mcheah/Rostock_Mini_Pro_2/sources_step/plate_spacer.step

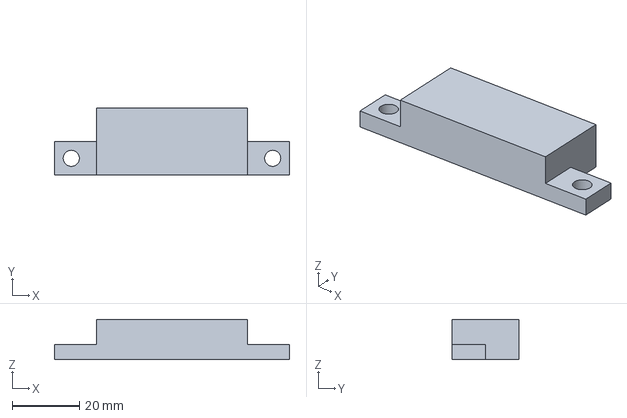
[picture p15: CAD file, 2026-03-06]
sources_step/plate_spacer.step
70.0 x 20.0 x 12.0 mm
