mcheah/Rostock_Mini_Pro_2/sources_step/filament_holder_topmount.step

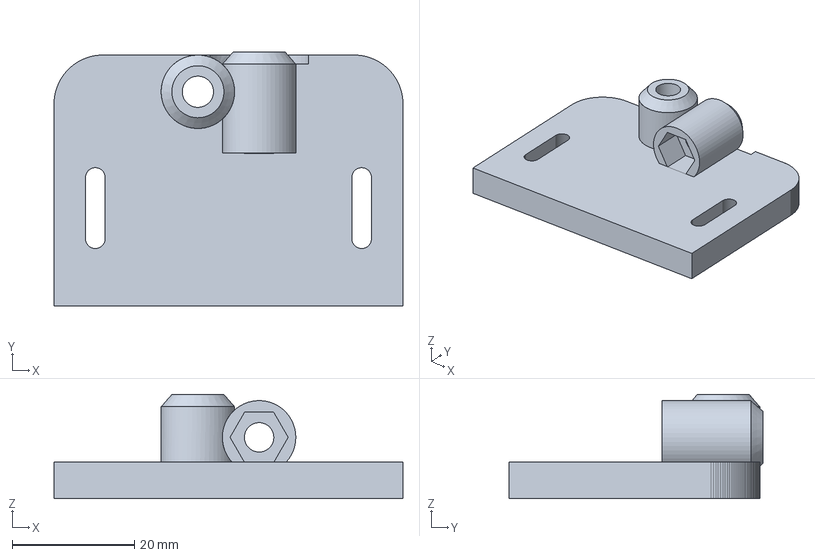
[picture p16: CAD file, 2026-03-06]
sources_step/filament_holder_topmount.step
57.0 x 41.5 x 17.0 mm
