mcheah/Rostock_Mini_Pro_2/sources_step/frame.step

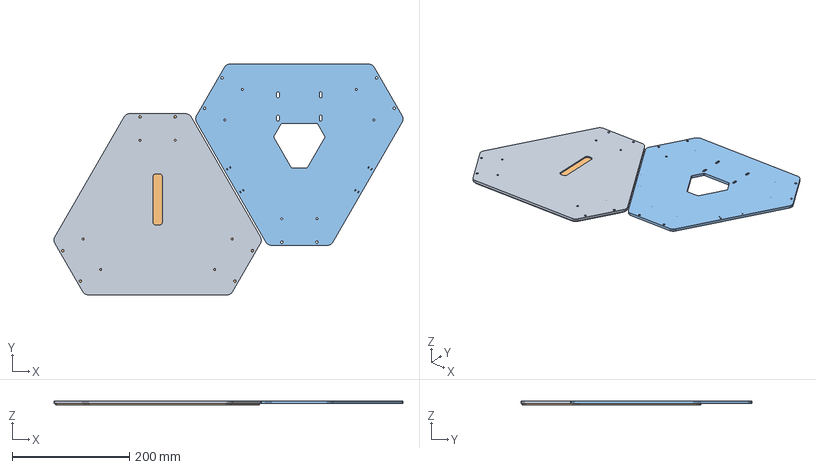
[picture p17: CAD file, 2026-03-06]
sources_step/frame.step
596.4 x 394.8 x 7.50 mm
minkowski003
