mcheah/Rostock_Mini_Pro_2/sources_step/endstop_template.step

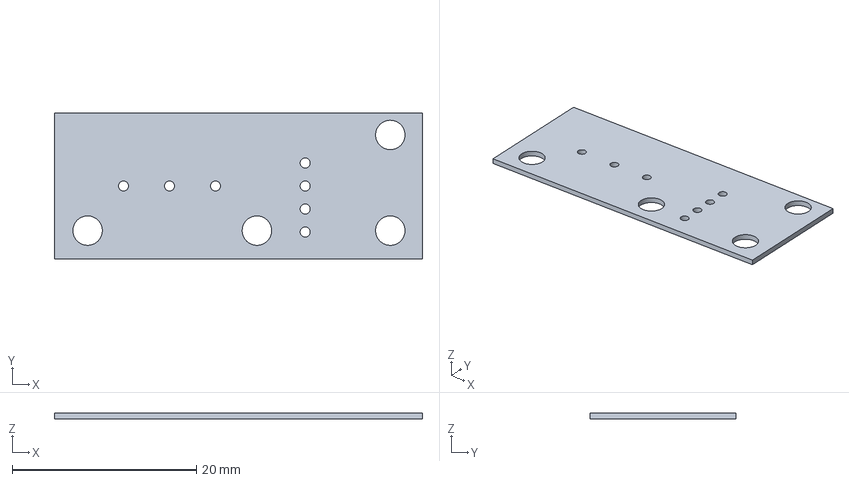
[picture p18: CAD file, 2026-03-06]
sources_step/endstop_template.step
40.0 x 15.9 x 0.65 mm
