mcheah/Rostock_Mini_Pro_2/sources_step/fan_mount.step

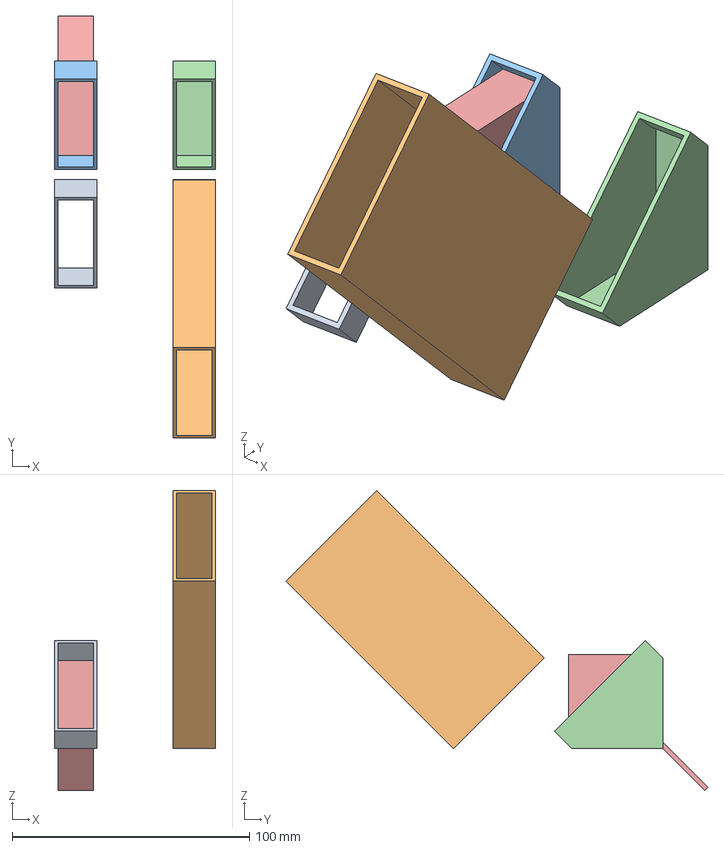
[picture p19: CAD file, 2026-03-06]
sources_step/fan_mount.step
68.0 x 178.1 x 126.6 mm
