mcheah/Rostock_Mini_Pro_2/sources_step/hotend_mount.step

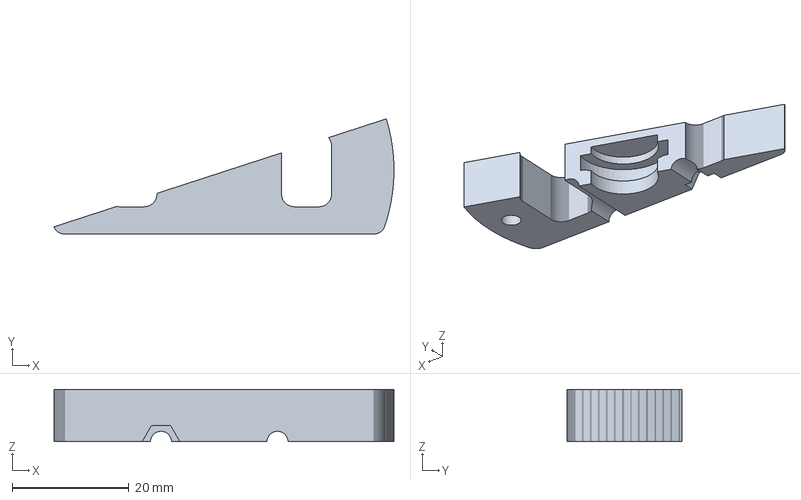
[picture p20: CAD file, 2026-02-26]
sources_step/hotend_mount.step
58.4 x 19.8 x 9.00 mm
