mcheah/Rostock_Mini_Pro_2/sources_step/hotend_mount_spacer.step

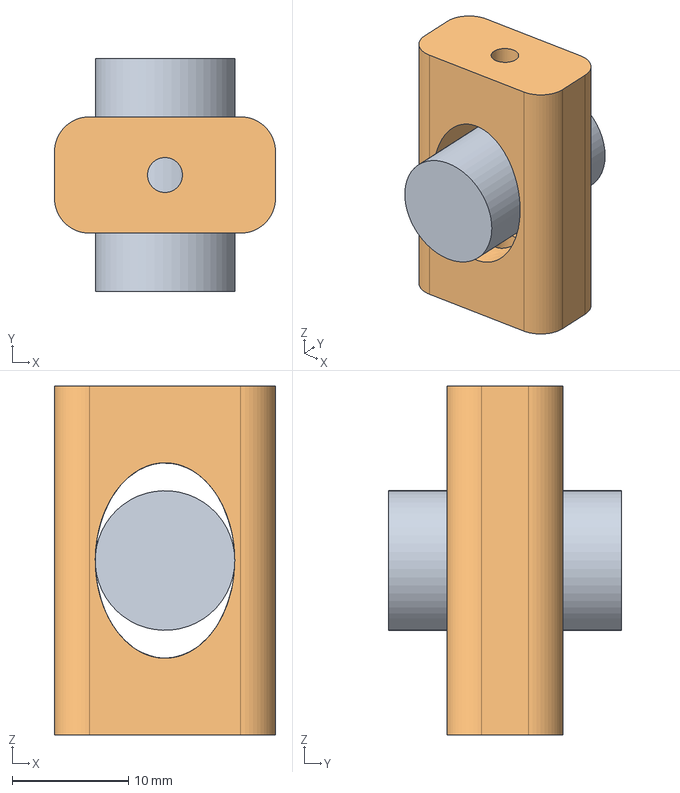
[picture p21: CAD file, 2026-02-26]
sources_step/hotend_mount_spacer.step
19.0 x 20.0 x 30.0 mm
