mcheah/Rostock_Mini_Pro_2/sources_step/plate_top.step

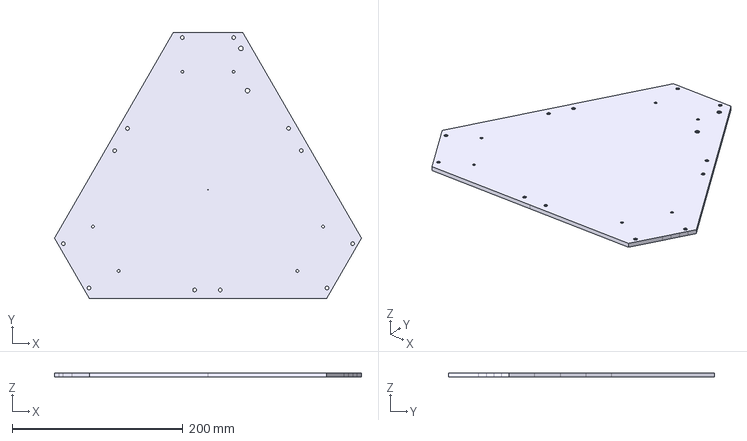
[picture p22: CAD file, 2026-02-26]
sources_step/plate_top.step
359.3 x 311.2 x 5.00 mm
