mcheah/Rostock_Mini_Pro_2/sources_step/motor_end_standoff.step

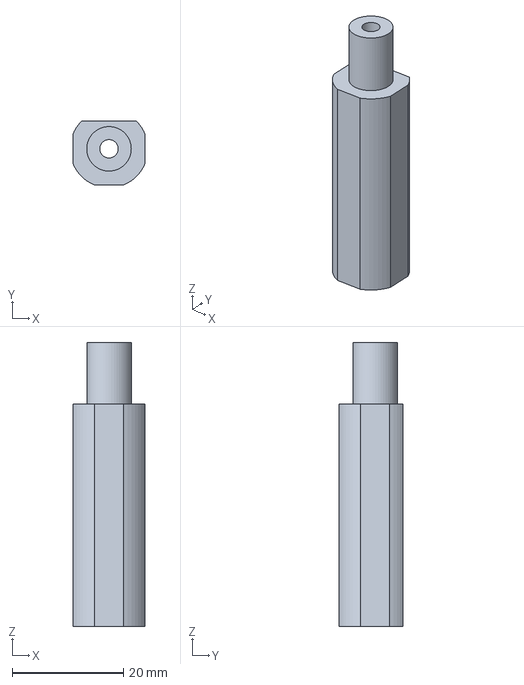
[picture p23: CAD file, 2026-02-26]
sources_step/motor_end_standoff.step
13.0 x 11.5 x 51.0 mm
