mcheah/Rostock_Mini_Pro_2/sources_step/filament_holder.step

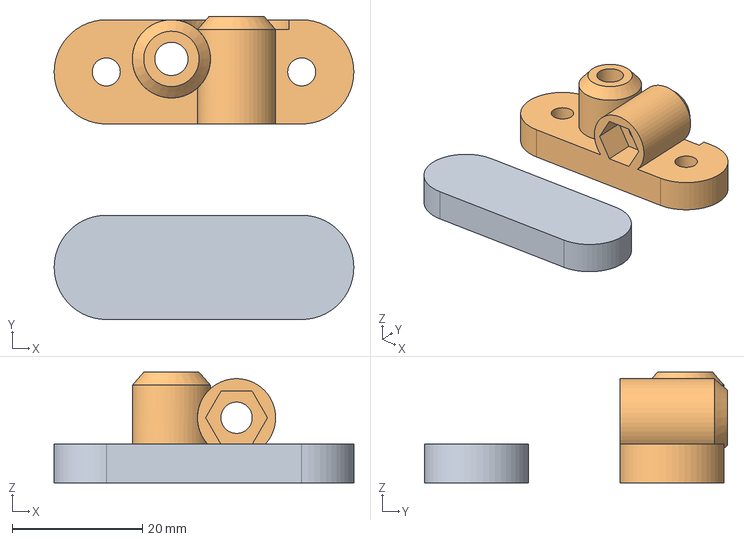
[picture p24: CAD file, 2026-02-26]
sources_step/filament_holder.step
46.0 x 46.5 x 17.0 mm
