mcheah/Rostock_Mini_Pro_2/sources_step/debug_drive_with_carriage.step

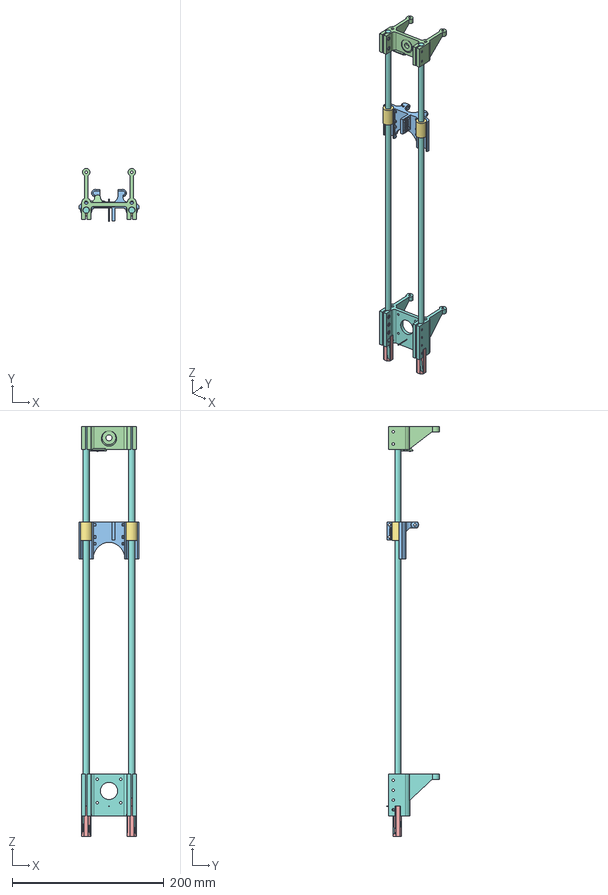
[picture p25: CAD file, 2026-02-26]
sources_step/debug_drive_with_carriage.step
79.0 x 70.0 x 540.0 mm
