mcheah/Rostock_Mini_Pro_2/sources_step/motor_end.step

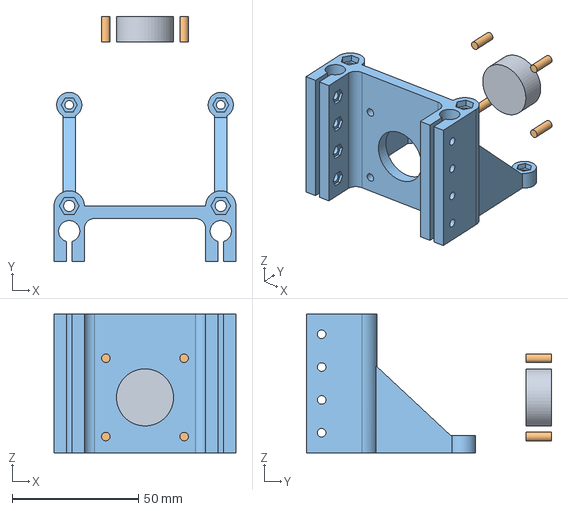
[picture p26: CAD file, 2026-02-26]
sources_step/motor_end.step
72.0 x 97.0 x 55.0 mm
