mcheah/Rostock_Mini_Pro_2/sources_step/belt_mount_for_carriage.step

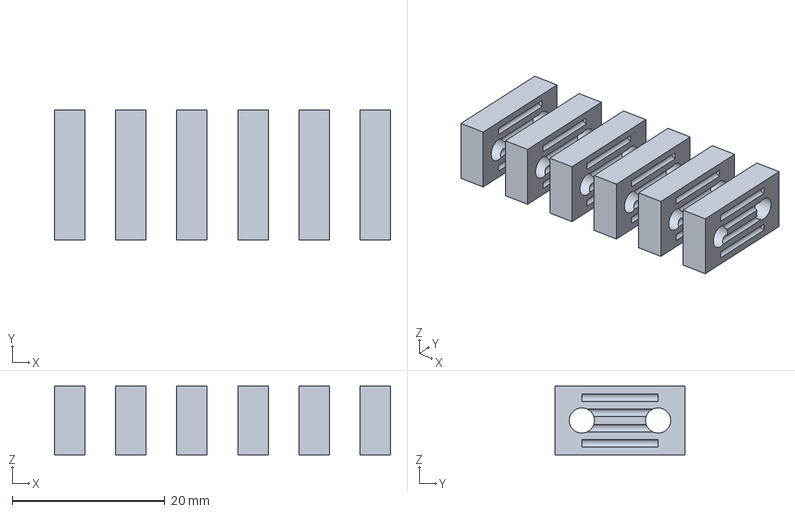
[picture p27: CAD file, 2026-02-26]
sources_step/belt_mount_for_carriage.step
44.0 x 17.0 x 9.00 mm
