mcheah/Rostock_Mini_Pro_2/sources_step/debug_platform_with_hotend_mount.step

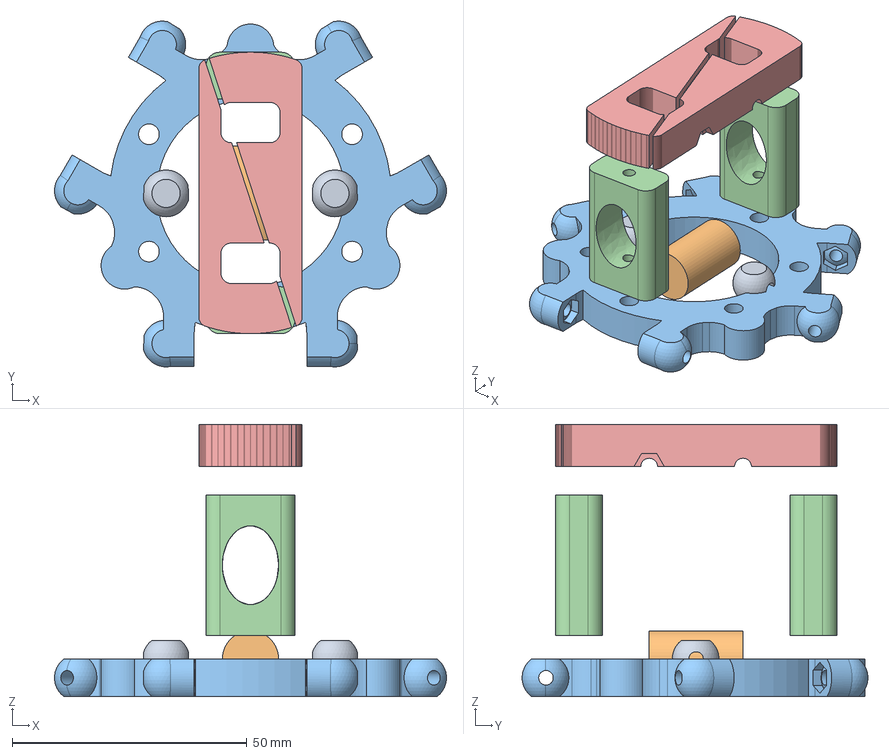
[picture p28: CAD file, 2026-02-26]
sources_step/debug_platform_with_hotend_mount.step
83.6 x 73.7 x 58.0 mm
