mcheah/Rostock_Mini_Pro_2/sources_openscad/bracket_inc.scad

rod_distance    = 60; // Smooth rod distance (center to center)
rod_hole_radius = 8.4/2;
