mcheah/Rostock_Mini_Pro_2/sources_openscad/idler_end.scad

/*
Info: 
This part sits at the upper end of the rods, below the top-plate. You need 3 of these.

Improvement:
- fins offers extra stability during the print (4 mounting screws instead of 2)
- direct mounting-platform for small hal-sensor-pcb

TODO: 
- give information on the hal-sensor-project

*/

idler_end_height = 30;
nn=5;
// Tilt bearings upward (the timing belt is pulling pretty hard).
// 2 degree tilt caused belts to slide off the bearings

tilt = -2; 
$fa=10;
$fs=0.1;
include <bracket_inc.scad> 
use <bracket.scad>
include <misc_parts_inc.scad>
use <misc_parts.scad>
use <prism.scad>
use <endstop_template.scad>

module bearing_mount() 
{
    rotate([90 - tilt, 0, 0]) union() 
    {  
        translate([0, 0, 2.3]) cylinder(r1=12, r2=9, h=1.1, center=true);
        translate([0, 0, -2.3]) cylinder(r1=9, r2=12, h=1.1, center=true);
    }
}
bearing_mount();

module bearing_mount_hole()  
{
    rotate([90 - tilt, 0, 0]) cylinder(r=4, h=40, center=true);
}
translate([0,30,0]) bearing_mount_hole();

// M_cutout can be used "sharpen" some parts by substracting an extruded M-Surface
// needed for the mag_zprobe_mount
module M_cutout(length, height, width, inner_width, offset) 
{
    margin = 5;
    x1=0;
    x2=height;
    x3=height+margin;
    y1=+width/2+margin;
    y2=+width/2;
    y3=offset+inner_width/2;
    y4=offset-inner_width/2;
    y5=-y2;
    y6=-y1;
    surface = [ [x3,y1],[x1,y1],[x1,y2],[x2,y3],[x2,y4], [x1,y5],[x1,y6], [x3,y6] ];
    rotate([0,-90,0]) prism(points=surface,height=length,center=true);     
}
 translate([0,80,0]) M_cutout(30,9,16,1,3);
 translate([0,120,0]) rotate([0,0,90]) M_cutout(30,9,24,10,0);


module mag_zprobe_mount() 
{
    h1 = 1;
    h2 = 10;
    translate([0,0,h2/2])
    difference()
    {
        difference() 
        {
            union() 
            {
                translate([ 0,6,0]) cube([16,12,h2], center=true);
                translate([+8,8,0]) cylinder(d=8,h=h2, center=true);
                translate([-8,8,0]) cylinder(d=8,h=h2, center=true);
                translate([ 0,0,0]) cylinder(d=8,h=h2, center=true);
                translate([ 0,0,0]) cylinder(d=3.0,h=h2+1.5, center=true);
            }
        // make it printable
            translate([0,4,h1-h2/2]) rotate([0,0,0])  M_cutout(30,h2-h1,16,1,3);
            translate([0,4,h1-h2/2]) rotate([0,0,90]) M_cutout(30,h2-h1,24,10,0);
        }
        translate([+8,0,0]) cylinder(d=8,h=h2+1, center=true);
        translate([-8,0,0]) cylinder(d=8,h=h2+1, center=true);
        translate([+8,8,0]) cylinder(d=3.4,h=h2+1, center=true);
        translate([-8,8,0]) cylinder(d=3.4,h=h2+1, center=true);
    }
}
// hi = idler_end_height; // Total height.
// wr = rod_distance;
translate([15,160,idler_end_height/2+2]) rotate([0,180,0]) rotate([0,0,180]) mag_zprobe_mount();

module mag_zprobe_mount_holes() 
{
    h = 8;
    translate([0,0,h/2]) union() 
    {
        translate([+8,8,0]) cylinder(d=3.4,h=h+1, center=true);
        translate([-8,8,0]) cylinder(d=3.4,h=h+1, center=true);
    }
}
translate([15,180,idler_end_height/2+2]) rotate([0,180,0]) rotate([0,0,180]) mag_zprobe_mount_holes();

module idler_end() 
{
	difference() {
	    hi = idler_end_height; // Total height.
	    wr = rod_distance;
	    translate([0, 0, hi/2]) difference() 
	    {
	        union() 
	        {
	            translate([0,0,nn/2]) bracket(hi+nn);
	            translate([+wr/2,10,-hi/2]) diagonal_fin2(hi,7, 40,30, 5);
	            translate([-wr/2,10,-hi/2]) diagonal_fin2(hi,7, 40,30, 5);
	            translate([0, 7.5, 0]) bearing_mount();
	        }
	 
	        translate([0, 8, 0]) bearing_mount_hole();
	    
	        for (i = [-1, 1]) for (z = [-8,8])
	            translate([i*(+wr/2-6),-6, z]) rotate([0,i*90,0]) screw_M3(25);
	    }
        //subtract holes to mount pcb endstop
        #translate([-23.5,0,(idler_end_height+nn)])
        color("green")
        rotate([270,0,0])
        mirror([0,0,0]) {
            #endstop_holes(50);
            translate([0,0,10.0015-2.1])
            pin_holes(50);
        }
    }
}

translate([0,200,0]) idler_end();
