mcheah/Rostock_Mini_Pro_2/sources_openscad/misc_parts_inc.scad

M3_screw_hole_dia = 3.4;
M3_nut_hole_dia   = 6.2+0.2;

M4_screw_hole_dia = 4.4;
M4_nut_hole_dia   = 7.7+0.2;

M5_screw_hole_dia = 5.4;
M5_nut_hole_dia   = 9.0+0.9;
